padilla107/ambu_project/Diseño/Proyección/001.JPG

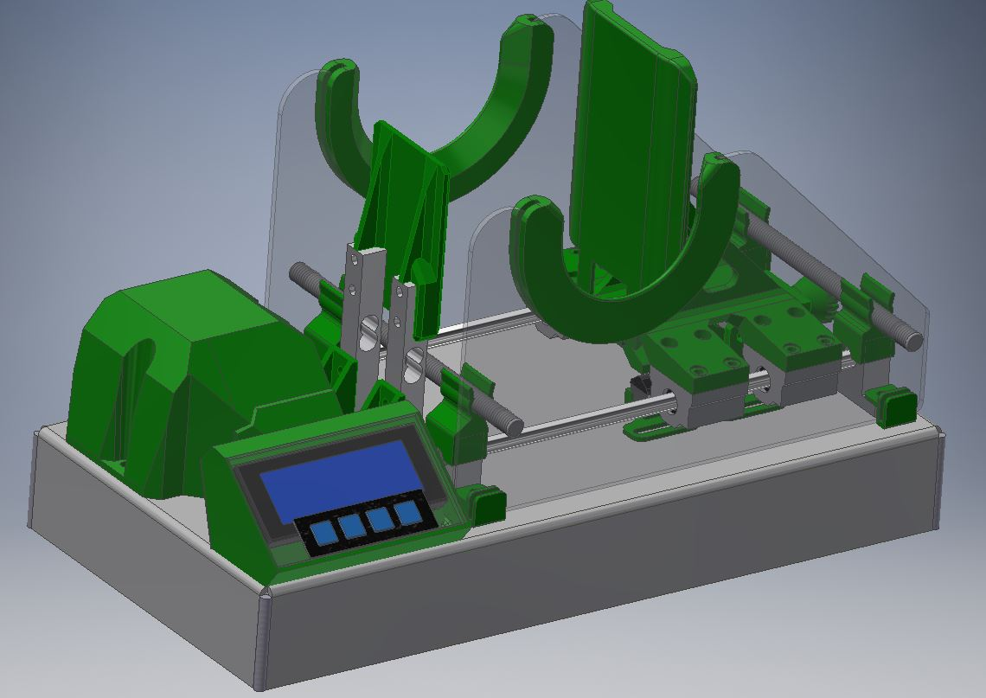
Diseño/Proyección/001.JPG
