padilla107/ambu_project/Diseño/Proyección/002.JPG

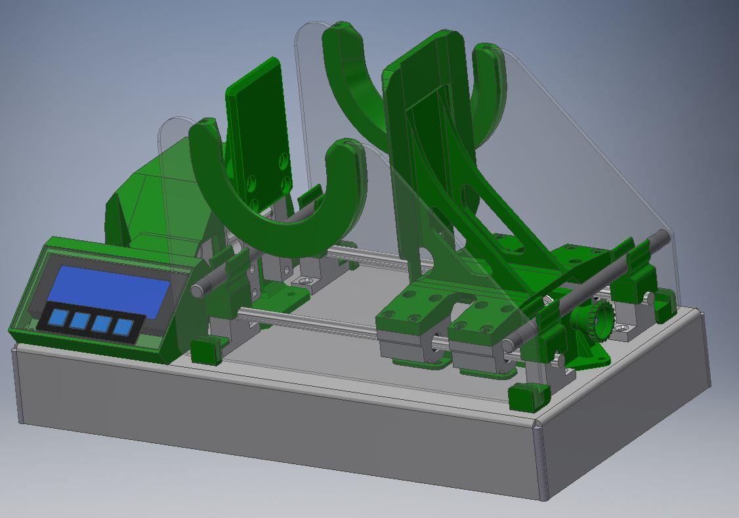
Diseño/Proyección/002.JPG
