padilla107/ambu_project/Diseño/Proyección/003.jpg

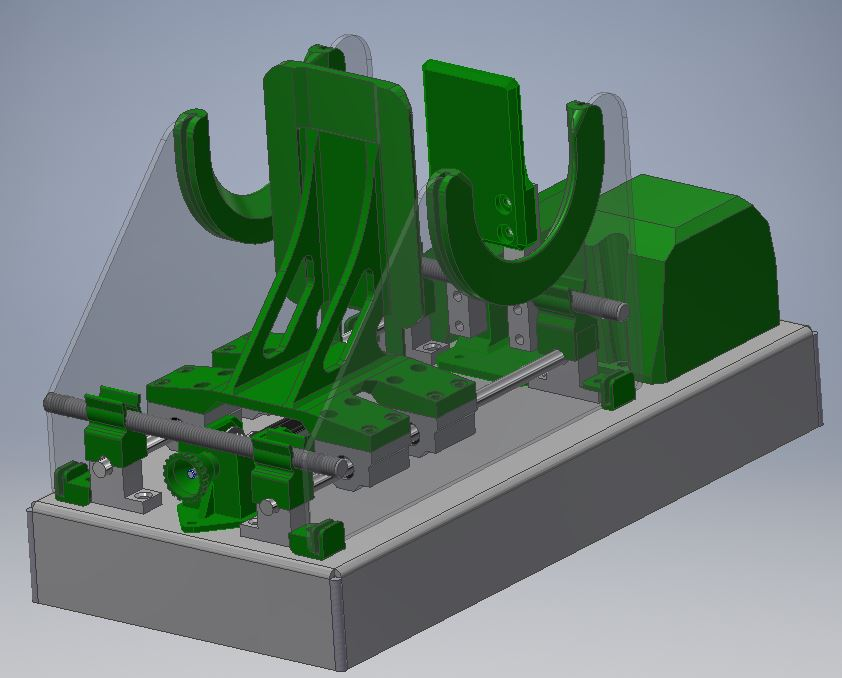
Diseño/Proyección/003.jpg
