padilla107/ambu_project/Diseño/Proyección/004.JPG

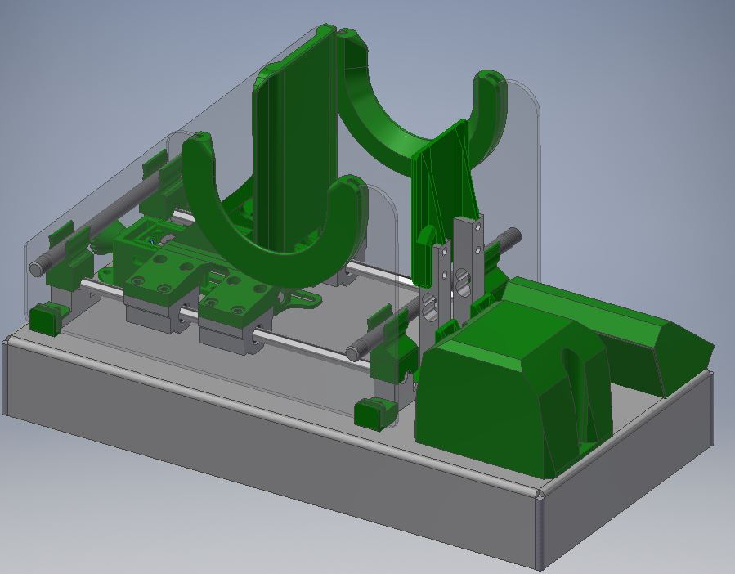
Diseño/Proyección/004.JPG
