padilla107/ambu_project/Diseño/Proyección/005.JPG

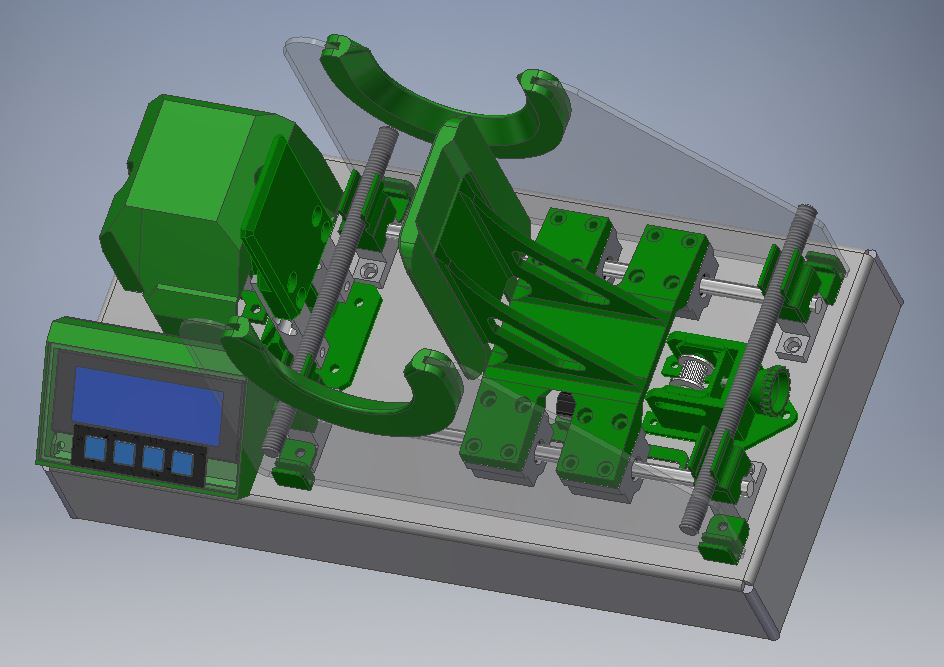
Diseño/Proyección/005.JPG
