padilla107/ambu_project/Diseño/Proyección/006.JPG

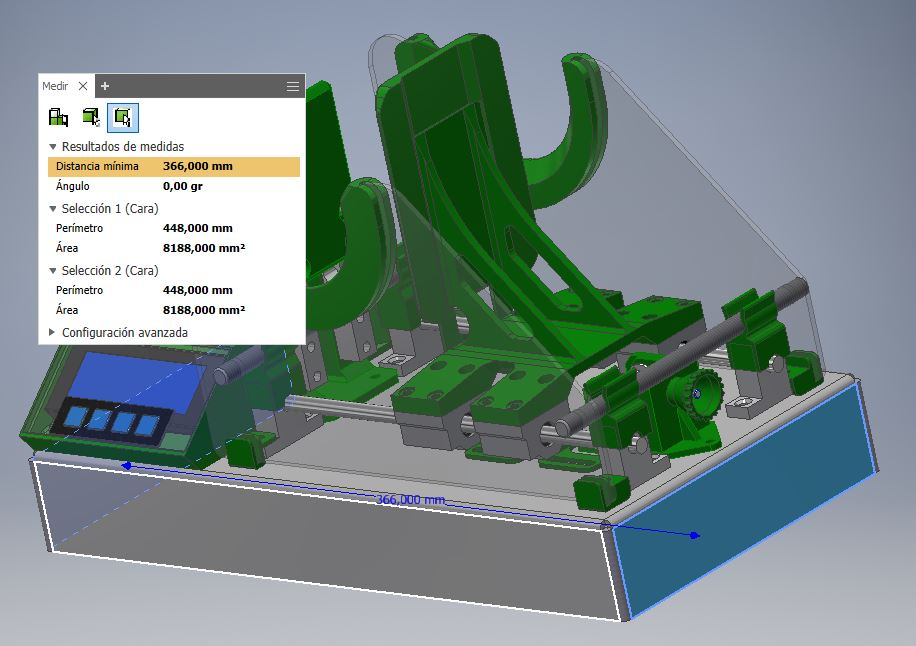
Diseño/Proyección/006.JPG
