padilla107/ambu_project/Diseño/Proyección/007.JPG

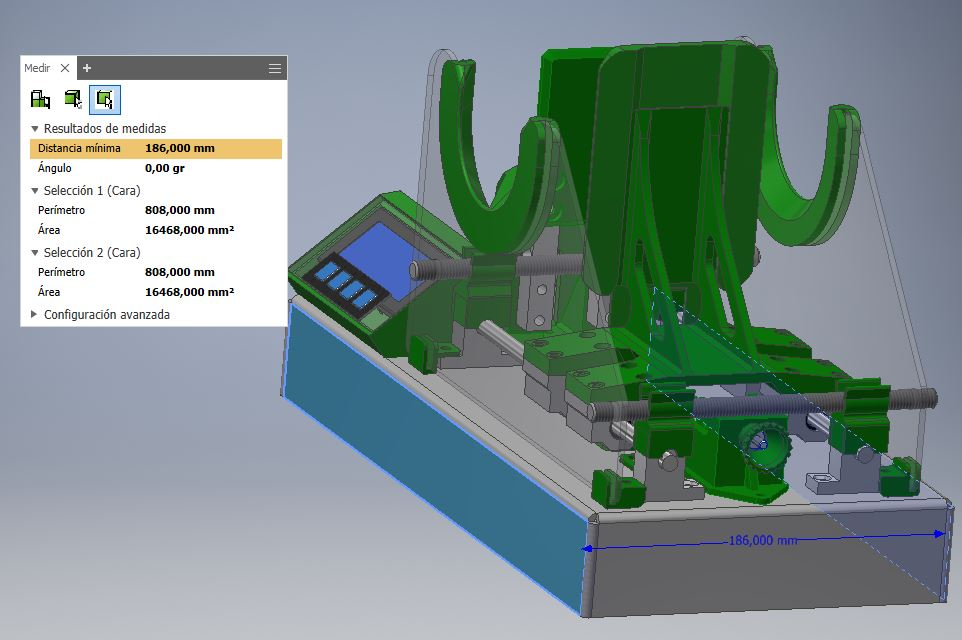
Diseño/Proyección/007.JPG
