padilla107/ambu_project/Diseño/Proyección/008.JPG

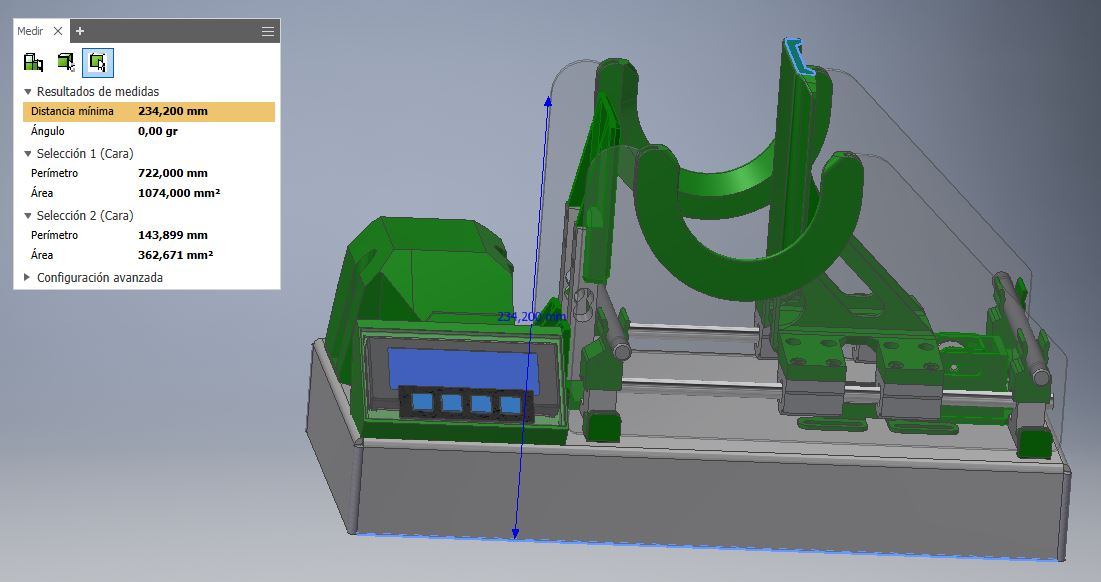
Diseño/Proyección/008.JPG
