padilla107/ambu_project/Diseño/Proyección/009.JPG

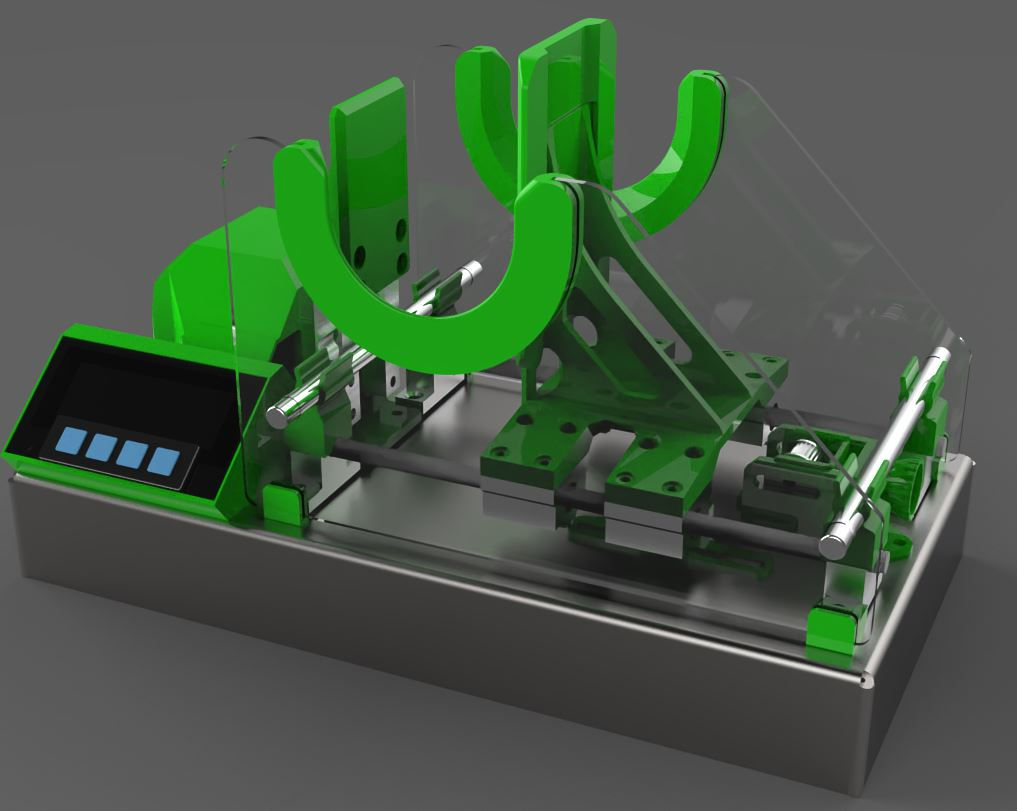
Diseño/Proyección/009.JPG
