padilla107/ambu_project/Diseño/Proyección/010.JPG

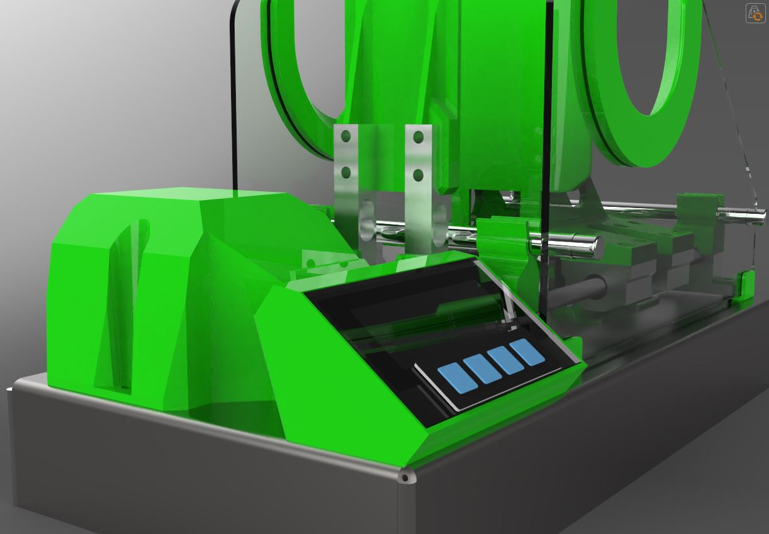
Diseño/Proyección/010.JPG
