padilla107/ambu_project/Diseño/Proyección/013.JPG

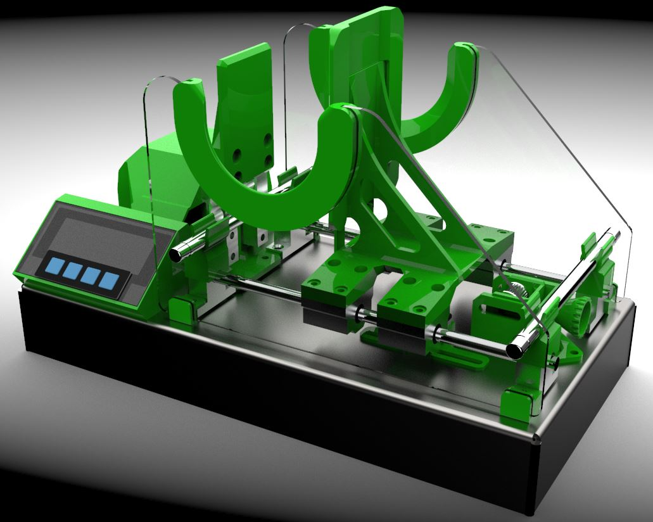
Diseño/Proyección/013.JPG
