padilla107/ambu_project/Diseño/Proyección/014.JPG

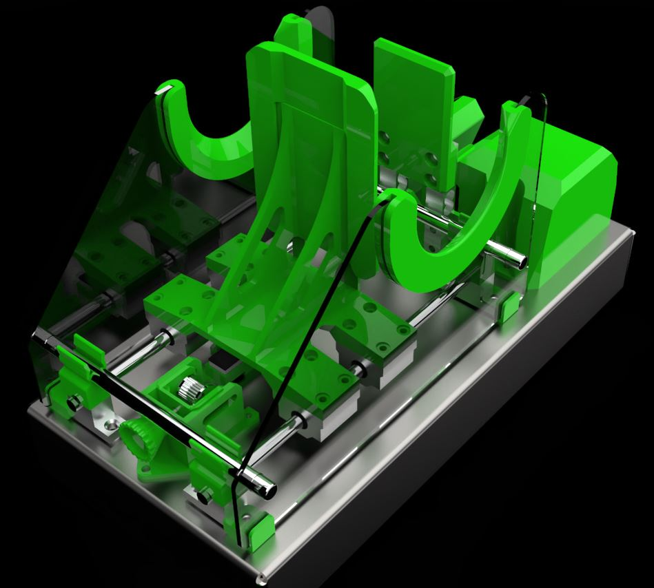
Diseño/Proyección/014.JPG
