padilla107/ambu_project/Diseño/Proyección/015.JPG

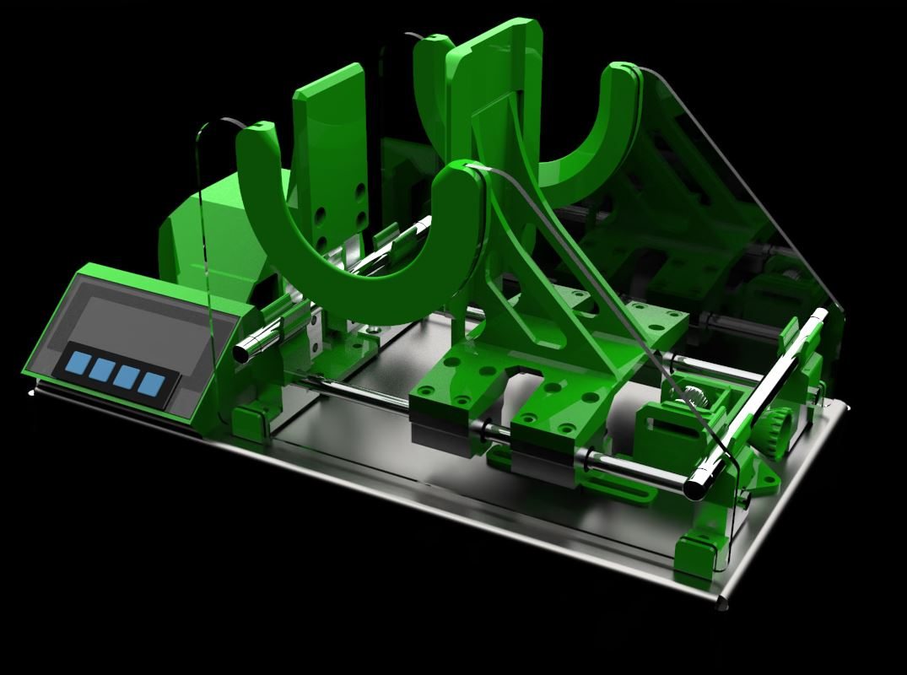
Diseño/Proyección/015.JPG
