padilla107/ambu_project/Diseño/Impresión 3D/Sujetador mica derecho.stl

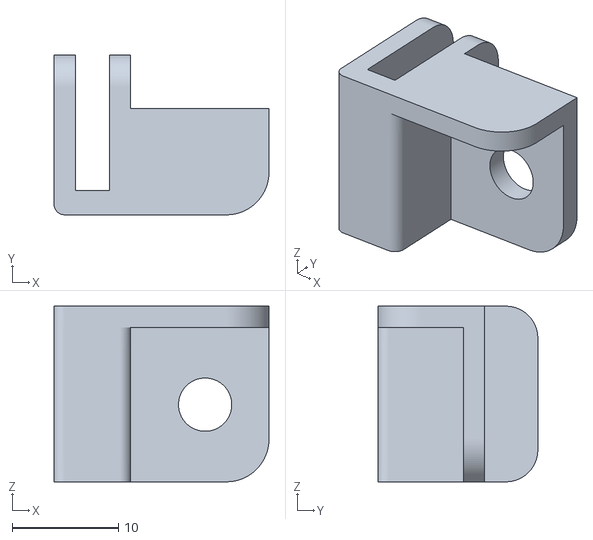
[picture p30: CAD file, 2024-09-11]
Diseño/Impresión 3D/Sujetador mica derecho.stl
20.2 x 15.0 x 16.5
