padilla107/ambu_project/Diseño/Impresión 3D/Cover motor.stl

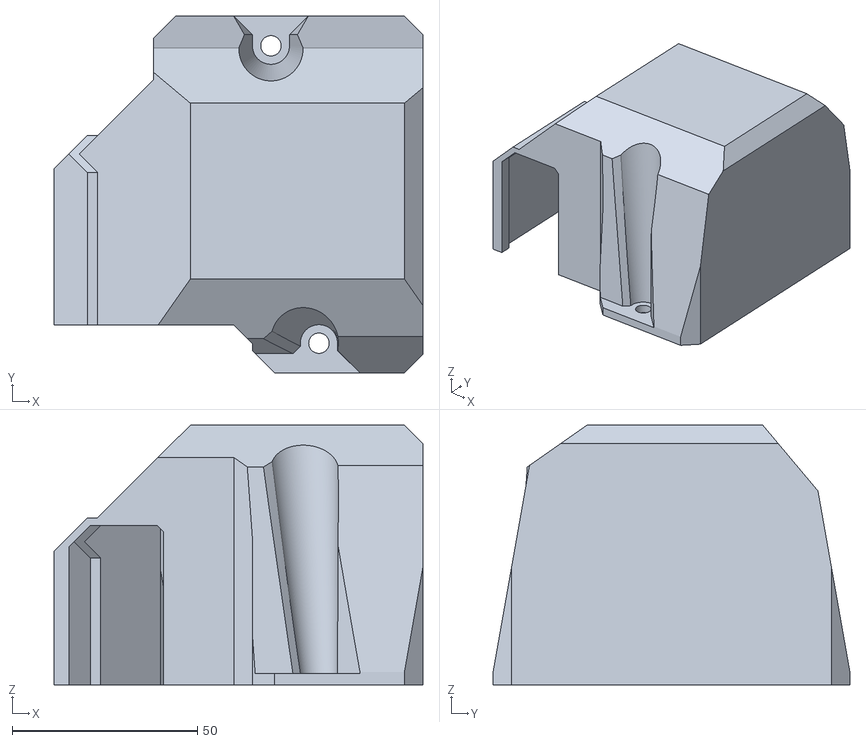
[picture p31: CAD file, 2024-09-11]
Diseño/Impresión 3D/Cover motor.stl
99.5 x 96.2 x 70.0
